printable-sleeve/printable-sleeve/files/cushion_XL.stl

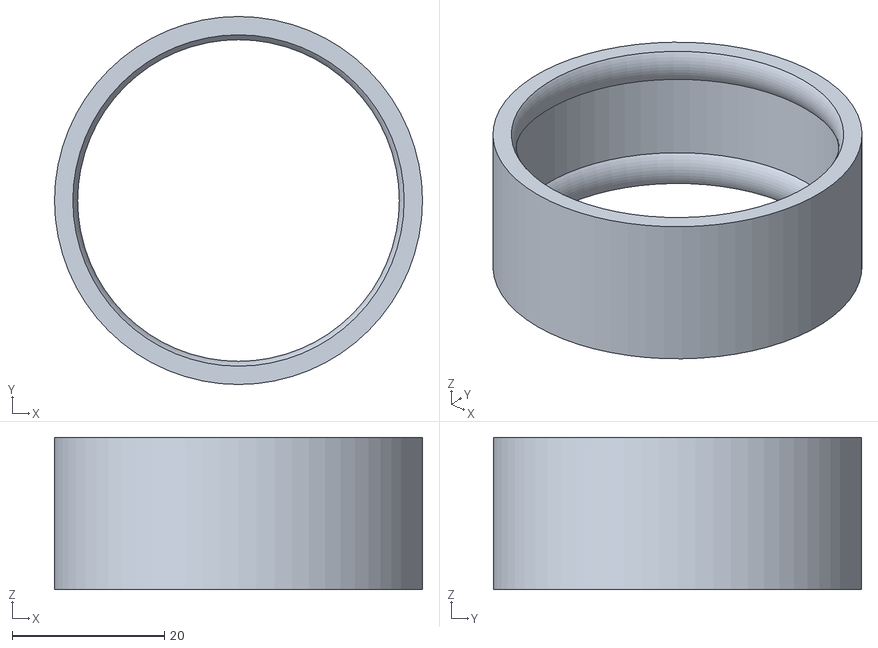
[picture p15: CAD file, 2026-04-25]
files/cushion_XL.stl
48.4 x 48.4 x 20.0
