printable-sleeve/printable-sleeve/files/inlay_S.stl

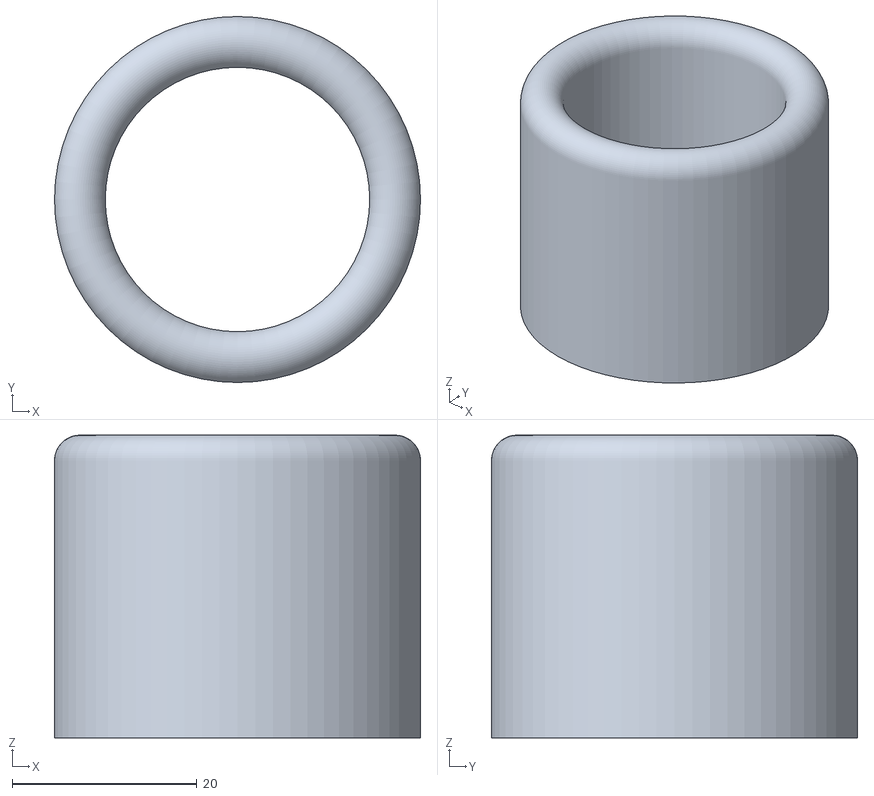
[picture p16: CAD file, 2026-04-25]
files/inlay_S.stl
39.6 x 39.6 x 32.8
