printable-sleeve/printable-sleeve/files/cap_XL.stl

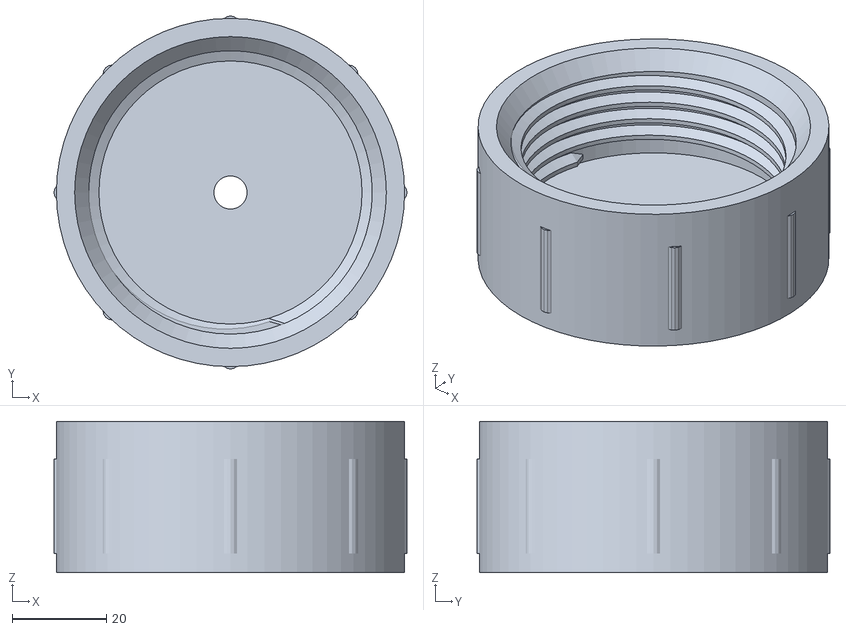
[picture p17: CAD file, 2026-04-25]
files/cap_XL.stl
74.8 x 74.8 x 32.0
